gheleguen/porte_a_poules/docs/pictures/PHOTO_20230718_234936.jpg

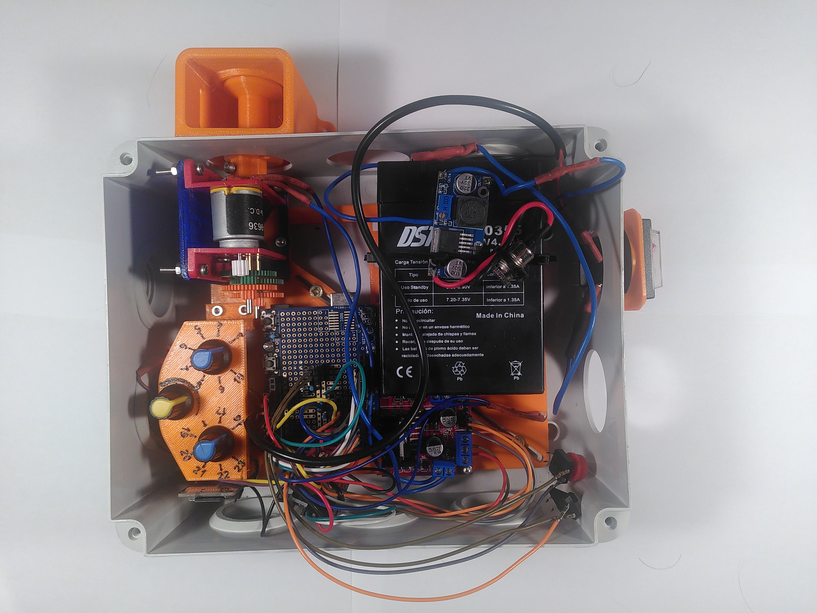
docs/pictures/PHOTO_20230718_234936.jpg
